maximyudayev/GS3440-adaptive-cable-equalizer/images/Eagle buildup.png

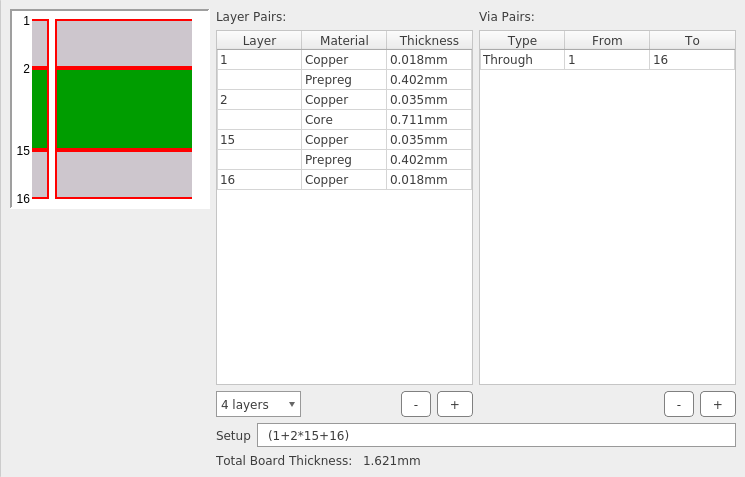
images/Eagle buildup.png
